Envious-Data/EnvOpenTorch/KiCad files/Mainboard/EnvLedTorch.kicad_sch

## KiCad design KiCad files/Mainboard/EnvLedTorch.kicad_sch (2023-12-31)

Schematic: EnvLedTorch.kicad_sch

Parts:
BAT1, BAT2, BAT3: Conn_01x02; SolderWire-2sqmm_1x02_P7.8mm_D2mm_OD3.9mm
C1, C2, C3, C6, C7, C8, C9, C10, C18, C35: 0.1uF 0402; C_0402_1005Metric
C4, C5: 330pF 0402; C_0402_1005Metric
C11: 2.2uF 0402; C_0402_1005Metric
C12, C13, C31, C32, C33, C34, C37, C38: 10uF 0603; C_0603_1608Metric
C14, C15: 50V 4.7uF 1210; C_1210_3225Metric
C16: 50V 10nF 1210; C_1210_3225Metric
C17: 100V 10nF 0603 X7R; C_0603_1608Metric
C19: 50V 2.2nF 0805; C_0805_2012Metric
C20: 50V 22pF 0603 C0G/NP0; C_0603_1608Metric
C21: TA 6.3V 100uF 1210; C_1210_3225Metric
C22, C23: 10V 47uF 1210; C_1210_3225Metric
C24, C25, C26: 10V 10uF 0402 X5R; C_0402_1005Metric
C27, C28: 35V 22uF 0805 X5R; C_0805_2012Metric
C29: 0.1uF 0402 X5R 35V; C_0402_1005Metric
C30: 35V 0.1uF 0402; C_0402_1005Metric
C36: 10uF 0402; C_0402_1005Metric
C39: 0.1uF 0603; C_0603_1608Metric
C40: 4.7uF 0603; C_0603_1608Metric
C41, C42: 0.047uF 0402; C_0402_1005Metric
C43, C45, C46, C47, C48, C58, C59: 50V 10uF 0805; C_0805_2012Metric
C44, C49: 50V 0.1uF 0402; C_0402_1005Metric
C50, C51: 50V 10uF 0603; C_0603_1608Metric
C52: 50V 1000pF 0402; C_0402_1005Metric
C53: 50V 4.7uF 0603 X5R; C_0603_1608Metric
C54, C55, C56, C57: 50V 0.01uF 0402 X7R; C_0402_1005Metric
D1: Diode, Schottky, 40 V, 5 A, SMC; D_SMC
D2: 0402 GREEN; LED_0402_1005Metric
IC1: BQ25792RQMR; Mouser Part Number 595-BQ25792RQMR
IC2: TPS25750DRJKR; Mouser Part Number 595-TPS25750DRJKR
J1: HRO_TYPE-C-31-M-12; USB_C_Receptacle_HRO_TYPE-C-31-M-12
J2: Conn_01x02; SolderWire-2sqmm_1x02_P7.8mm_D2mm_OD3.9mm
J3, J6: Aardvark; PinHeader_2x05_P2.54mm_Vertical
J4: SYS/GND; PinHeader_1x02_P2.54mm_Vertical
J5: BAT/GND; PinHeader_1x02_P2.54mm_Vertical
J7: THERMISTOR / GND; PinHeader_1x02_P2.54mm_Vertical
J8: TS/NORM; PinHeader_1x02_P2.54mm_Vertical
J9: 2S/1.5MHz/2A ICGH; PinHeader_1x02_P2.54mm_Vertical
J10: 3S/1.5MHz/1A ICGH; PinHeader_1x02_P2.54mm_Vertical
J11: 4S/1.5MHz/1A ICGH; PinHeader_1x02_P2.54mm_Vertical
L1: 9.5A 4.7uH 15m 1050; L_Wuerth_HCI-1050
L2: IHLP2020BZER1R0M11; L_Vishay_IHLP-2020
NT1: NetTie; NetTie-2_SMD_Pad2.0mm
PS1: TPS54531DDAR; SOIC127P600X170-9N; Mouser Part Number 595-TPS54531DDAR
Q1, Q2, Q3: BSP89; SOT-223-3_TabPin2
Q4, Q5: AO3401A; SOT-23
R1, R4, R6: 47 2512; R_2512_6332Metric
R2, R3, R5: 100 0805; R_0805_2012Metric
R7: 665K 0603; R_0603_1608Metric
R8: 130K 0603; R_0603_1608Metric
R9: 37.4K 0603; R_0603_1608Metric
R10: 0603; R_0603_1608Metric
R11: 10.2K 0603; R_0603_1608Metric
R12: 1.96K 0603; R_0603_1608Metric
R13, R14, R30, R31, R38: 2.2K 0402; R_0402_1005Metric
R15, R16, R17, R28, R35: 10K 0402; R_0402_1005Metric
R18, R19, R20, R25, R26, R27: 1K 0402; R_0402_1005Metric
R21, R22: 5.1K 0402; R_0402_1005Metric
R23: 1M 0402; R_0402_1005Metric
R24: 0r 2512; R_2512_6332Metric
R29: 100 0603; R_0603_1608Metric
R32: 10.0 1206; R_1206_3216Metric
R33: 5.23K 0402; R_0402_1005Metric
R34: 30.1K 0402; R_0402_1005Metric
R36: 137K 0603; R_0603_1608Metric
R37: 100K 0603; R_0603_1608Metric
R39: 6.04K 0603; R_0603_1608Metric
R40: 10.5K 0603; R_0603_1608Metric
R41: 17.4K 0603; R_0603_1608Metric
R103: 51r 2512; R_2512_6332Metric
U1, U2, U3: HY2213; SOT-23-6
U4: TLV75533PDBV; SOT-23-5
U5: TVS2200DRV; WSON-6-1EP_2x2mm_P0.65mm_EP1x1.6mm
U6: CAT24C256; MSOP-8-1EP_3x3mm_P0.65mm_EP1.68x1.88mm
U9: 8254; HTSSOP-16-1EP_4.4x5mm_P0.65mm_EP3.4x5mm

Connections:
+12V: J2.1, Q4.2 (S), R22.2, R23.2
BTST1: C41.1, IC1.4 (BTST1)
BTST2: C42.1, IC1.19 (BTST2)
DRAIN: IC2.15 (DRAIN_1), IC2.30 (DRAIN_2), IC2.40 (DRAIN_3)
GND: C4.2, C5.2, C12.2, C13.2, C14.2, C15.2, C16.2, C17.2, C20.2, C21.2, C22.2, C23.2, C24.2, C25.2, C26.2, C27.2, C28.2, C29.2, C30.2, C31.2, C32.2, C33.2, C34.2, C35.2, C36.2, C37.2, C38.2, C39.2, C40.2, C43.2, C44.2, C45.2, C46.2, C47.2, C48.2, C49.2, C50.2, C51.2, C53.2, C54.2, C55.2, C56.2, C57.2, C58.2, C59.2, D1.2 (A), IC1.27 (GND), IC2.10 (I2CS_IRQ), IC2.11 (GND_1), IC2.12 (GND_2), IC2.14 (GND_3), IC2.18 (I2CM_IRQ), IC2.31 (GND_4), IC2.39 (GND_5), J1.A1 (GND), J1.A12 (GND), J1.B1 (GND), J1.B12 (GND), J1.S1 (SHIELD), J2.2, J3.2, J3.10, J4.2, J5.2, NT1.1, PS1.7 (GND), PS1.9 (EP), R8.1, R9.1, R12.1, R15.1, R16.1, R17.1, R20.1, R24.1, R28.1, U4.2 (GND), U5.1 (GND), U5.2 (GND), U5.3 (GND), U5.7 (GND), U6.4 (GND)
GNDA: C52.2, IC1.10 (ACDRV2), IC1.11 (ACDRV1), IC1.13 (~CE), J6.6, J7.2, NT1.2, R34.1, R35.1, R37.1, R39.1, R40.1, R41.1
I2C1_SCL: IC2.9 (I2CS_SCL), J6.9, R31.1
I2C1_SDA: IC2.8 (I2CS_SDA), J6.10, R30.1
I2C_SCL: IC1.14 (SCL), IC2.17 (I2CM_SCL), J3.1, R13.1, U6.6 (SCL)
I2C_SDA: IC1.15 (SDA), IC2.16 (I2CM_SDA), J3.3, R14.1, U6.5 (SDA)
ILIM_HIZ: IC1.17 (ILIM_HIZ), R36.1, R37.2
LDO_1V5: C26.1, IC2.2 (ADCIN1), IC2.3 (ADCIN2), IC2.4 (LDO_1V5)
LDO_3V3: C25.1, C30.1, IC2.1 (LDO_3V3), R13.2, R14.2, R30.2, R31.2, R38.2, U6.8 (VCC)
unnamed: BAT1.1, BAT2.2, C2.2, Q2.3 (S), R1.1, R2.1, R25.2, U2.3 (VSS)
unnamed: BAT1.2, C1.2, Q1.3 (S), R19.2, R103.1, U1.3 (VSS)
unnamed: BAT2.1, BAT3.2, C3.2, Q3.3 (S), R3.1, R4.1, R26.2, U3.3 (VSS)
unnamed: C1.1, R2.2, U1.2 (VDD)
unnamed: C2.1, R3.2, U2.2 (VDD)
unnamed: C3.1, R5.2, U3.2 (VDD)
unnamed: C6.2, R27.1, U9.15 (VCC1)
unnamed: C7.2, R26.1, U9.14 (VCC2)
unnamed: C8.2, R25.1, U9.13 (VCC3)
unnamed: C9.1, U9.6 (CCT)
unnamed: C10.1, U9.5 (CDT)
unnamed: C17.1, PS1.4 (SS)
unnamed: C18.1, D1.1 (K), L1.1, PS1.8 (PH)
unnamed: C18.2, PS1.1 (BOOT)
unnamed: C19.1, C20.1, PS1.6 (COMP)
unnamed: C19.2, R9.2
unnamed: C49.1, C50.1, C51.1, IC1.22 (BAT_1), IC1.23 (BAT_2), J5.1, R29.1
unnamed: D2.2 (A), R38.1
unnamed: IC1.18 (BATP), R29.2
unnamed: J6.5, R32.1
unnamed: J8.2, R35.2
unnamed: J9.2, R39.2
unnamed: J10.2, R40.2
unnamed: J11.2, R41.2
unnamed: PS1.3 (EN), R7.1, R8.2
unnamed: PS1.5 (VSENSE), R11.1, R12.2
unnamed: Q1.1 (G), U1.6 (Out)
unnamed: Q1.2 (D), R1.2
unnamed: Q2.1 (G), U2.6 (Out)
unnamed: Q2.2 (D), R4.2
unnamed: Q3.1 (G), U3.6 (Out)
unnamed: Q3.2 (D), R6.2
unnamed: Q4.1 (G), R23.1, U9.1 (COP)
unnamed: Q4.3 (D), Q5.3 (D)
unnamed: Q5.1 (G), R21.2
unnamed: R10.1, R11.2
unnamed: R15.2, U6.3 (A2)
unnamed: R16.2, U6.2 (A1)
unnamed: R17.2, U6.1 (A0)
unnamed: R18.1, U9.10 (SEL)
unnamed: R19.1, U9.11 (CTL)
unnamed: R20.2, U9.4 (VINI)
unnamed: R21.1, U9.3 (DOP)
unnamed: R22.1, U9.2 (VMP)
unnamed: R28.2, U6.7 (WP)
P3V3: C13.1, C24.1, IC2.38 (VIN_3V3), R32.2, U4.5 (OUT)
PMID: C36.1, C37.1, C38.1, C39.1, IC1.29 (PMID)
PP5V: C12.1, C21.1, C22.1, C23.1, IC2.34 (PP5V_1), IC2.35 (PP5V_2), IC2.44 (PP5V_3), L1.2, R10.2, U4.1 (IN), U4.3 (EN)
PPHV: C27.1, C28.1, C29.1, C31.1, C32.1, C33.1, C34.1, C35.1, IC1.2 (VBUS_1), IC1.3 (VBUS_2), IC1.8 (VAC2), IC1.9 (VAC1_1), IC1.31 (VAC1_2), IC2.20 (PPHV_1), IC2.21 (PPHV_2), IC2.22 (PPHV_3), IC2.41 (PPHV_4)
PROG: IC1.20 (PROG), J9.1, J10.1, J11.1
REGN: C40.1, IC1.5 (REGN), R33.2, R36.2
SDRV: C52.1, IC1.24 (SDRV_1), IC1.33 (SDRV_2)
STAT: D2.1 (K), IC1.1 (STAT_1), IC1.30 (STAT_2)
SW1: C41.2, IC1.28 (SW1), L2.1
SW2: C42.2, IC1.26 (SW2), L2.2
SYS: C14.1, C15.1, C16.1, C43.1, C44.1, C45.1, C46.1, C47.1, C48.1, C58.1, C59.1, IC1.25 (SYS), J4.1, PS1.2 (VIN), R7.2
TS: IC1.16 (TS_1), IC1.32 (TS_2), J7.1, J8.1, R33.1, R34.2
USB_CC1: C4.1, IC2.28 (CC1), J1.A5 (CC1)
USB_CC2: C5.1, IC2.29 (CC2), J1.B5 (CC2)
USB_D+: IC2.26 (GPIO4/USB_P), J1.A6 (D+), J1.B6 (D+)
USB_D-: IC2.27 (GPIO5/USB_N), J1.A7 (D-), J1.B7 (D-)
USB_VBUS: C53.1, C54.1, C55.1, C56.1, C57.1, IC2.23 (VBUS_IN_1), IC2.24 (VBUS_IN_2), IC2.25 (VBUS_IN_3), IC2.32 (VBUS_1), IC2.33 (VBUS_2), IC2.42 (VBUS_IN_4), IC2.43 (VBUS_3), J1.A4 (VBUS), J1.A9 (VBUS), J1.B4 (VBUS), J1.B9 (VBUS), U5.4 (IN), U5.5 (IN), U5.6 (IN)
VDD: BAT3.1, C6.1, C7.1, C8.1, C11.1, Q5.2 (S), R5.1, R6.1, R27.2, U9.16 (VDD)
VSS: C9.2, C10.2, C11.2, R18.2, R24.2, R103.2, U9.7 (VSS), U9.12 (VCC4)

Notes on the sheet:
OLD CIRCUIT
RCTL
RSENSE
Need to swap for BQ25731 eventually
RVSS
